DerPhysikeR/Original-Prusa-i3/Printed-Parts/scad/Y-distance.scad

// PRUSA iteration3
// X carriage
// GNU GPL v3
// Josef Průša <iam@josefprusa.cz> and contributors
// http://www.reprap.org/wiki/Prusa_Mendel
// http://prusamendel.org

difference()
{

//body
union()
{
    translate([3,-19,0]) cube([5,37,10]);
    translate([8,-19,0]) cube([4,37,10]);
}


union()
{
    //rods
    translate(v = [4,-11,-1]) cylinder(h = 12, r=5, $fn=50);	
    translate(v = [4,10,-1]) cylinder(h = 12, r=5, $fn=50);
    //cables
    translate([10,5,3]) cube([8,9,10]);
}

        //corners
        translate([-5,24,3]) rotate([45,0,0]) cube([20,10,10]);
        translate([-5,24,-7]) rotate([45,0,0]) cube([20,10,10]);
        translate([-5,-25,3]) rotate([45,0,0]) cube([20,10,10]);
        translate([-5,-25,-7]) rotate([45,0,0]) cube([20,10,10]);
}
