DerPhysikeR/Original-Prusa-i3/Printed-Parts/scad/z-screw-cover.scad

// PRUSA iteration3
// Z screw cover
// GNU GPL v3
// Josef Průša <iam@josefprusa.cz> and contributors
// http://www.reprap.org/wiki/Prusa_Mendel
// http://prusamendel.org


/* translate(v=[-2.5, 0, 4.3]) rotate([0,90,0])  cylinder(r1=0.6, r2=0.4, h = 1, $fn=60); */
/* translate(v=[2.5, 0, 4.3]) rotate([0,-90,0])  cylinder(r1=0.6, r2=0.4, h = 1, $fn=60); */
/* translate(v=[0, 2.5, 4.3]) rotate([90,0,0])  cylinder(r1=0.6, r2=0.4, h = 1, $fn=60); */
/* translate(v=[0, -2.5, 4.3]) rotate([-90,0,0])  cylinder(r1=0.6, r2=0.4, h = 1, $fn=60); */

/* translate(v=[-2.5, 0.5, 4.0]) rotate([0,90,0])  cylinder(r1=0.6, r2=0.3, h = 0.8, $fn=60); */
/* translate(v=[2.5, -0.5, 4.0]) rotate([0,-90,0])  cylinder(r1=0.6, r2=0.3, h = 0.8, $fn=60); */
/* translate(v=[0.5, 2.5, 4.0]) rotate([90,0,0])  cylinder(r1=0.6, r2=0.3, h = 0.8, $fn=60); */
/* translate(v=[-0.5, -2.5, 4.0]) rotate([-90,0,0])  cylinder(r1=0.6, r2=0.3, h = 0.8, $fn=60); */

/* translate(v=[-2.5, 1, 3.7]) rotate([0,90,0])  cylinder(r1=0.5, r2=0.3, h = 0.6, $fn=60); */
/* translate(v=[2.5, -1, 3.7]) rotate([0,-90,0])  cylinder(r1=0.5, r2=0.3, h = 0.6, $fn=60); */
/* translate(v=[1, 2.5, 3.7]) rotate([90,0,0])  cylinder(r1=0.5, r2=0.3, h = 0.6, $fn=60); */
/* translate(v=[-1, -2.5, 3.7]) rotate([-90,0,0])  cylinder(r1=0.5, r2=0.3, h = 0.6, $fn=60); */

difference()
{
    union()
        {
            translate(v=[0, 0, 1]) cylinder(r1=8, r2=4.6, h = 4);
            cylinder(r=8, h = 1, $fn=60);
        }
        translate(v=[0, 0, -1]) cylinder(r=2.5, h = 7, $fn=60);
        cylinder(r=2.5, h = 1, $fn=60);
}
